deets/new-joy-tracker/src/debugpin.py

import machine
import newjoy

BOOT_PIN = 0
DEBUG_MODE = False


def toggle_debug(pin):
    global DEBUG_MODE
    DEBUG_MODE = not DEBUG_MODE
    print("max_task_time", newjoy.max_task_time())


def setup():
    p = machine.Pin(
        BOOT_PIN,
        machine.Pin.IN,
        machine.Pin.PULL_UP,
    )
    p.irq(trigger=machine.Pin.IRQ_FALLING, handler=toggle_debug)
